lukasznowarkiewicz/low-profile-cpu-cooling-solution-research/Attachments/DD7BBE43-BE83-4B21-8B71-0276DDDCC2B3.png

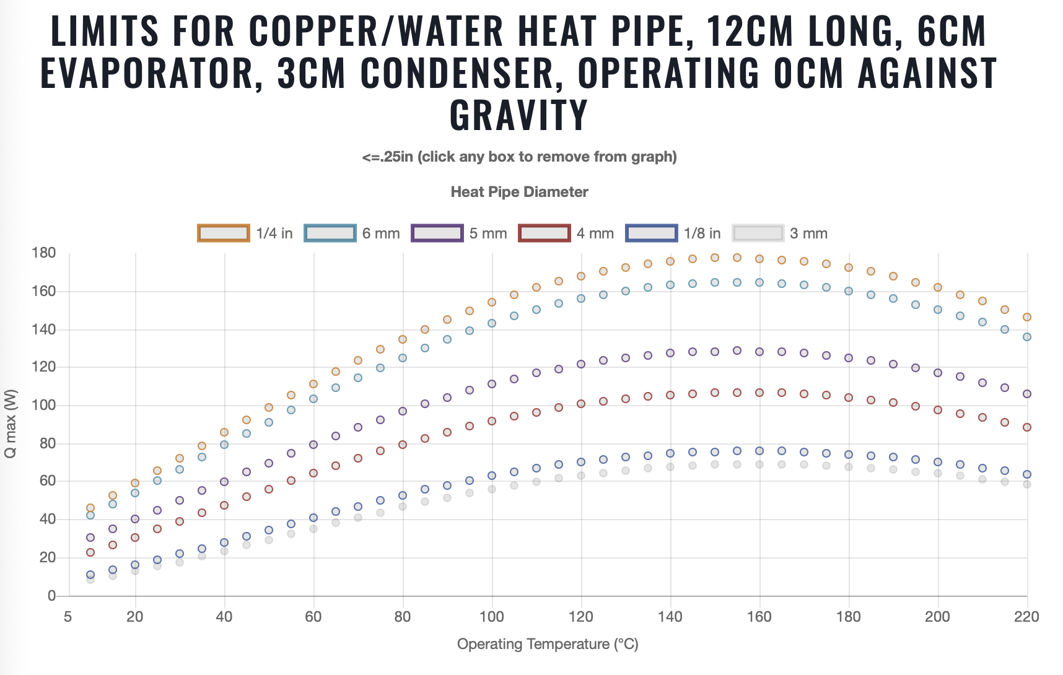
Attachments/DD7BBE43-BE83-4B21-8B71-0276DDDCC2B3.png
