lukasznowarkiewicz/low-profile-cpu-cooling-solution-research/tests recordings/series 1/Screenshot (21).png

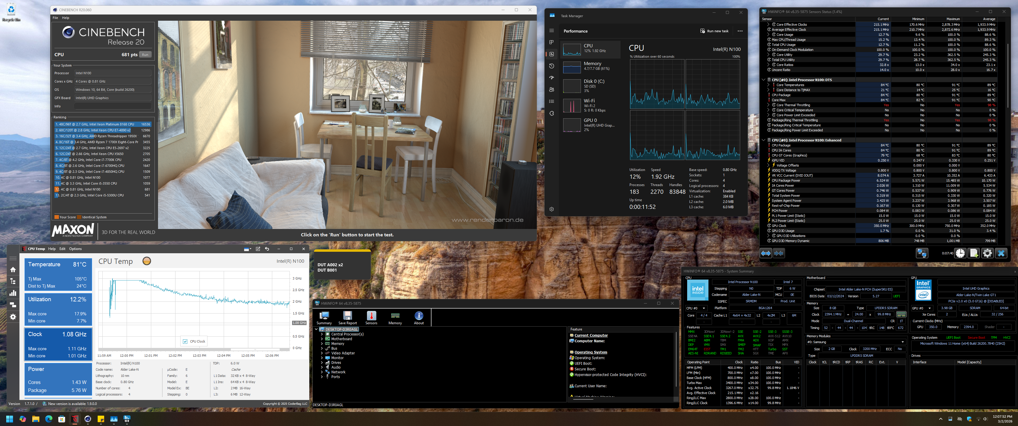
tests recordings/series 1/Screenshot (21).png
