lukasznowarkiewicz/low-profile-cpu-cooling-solution-research/tests recordings/series 3/Screenshot (115).png

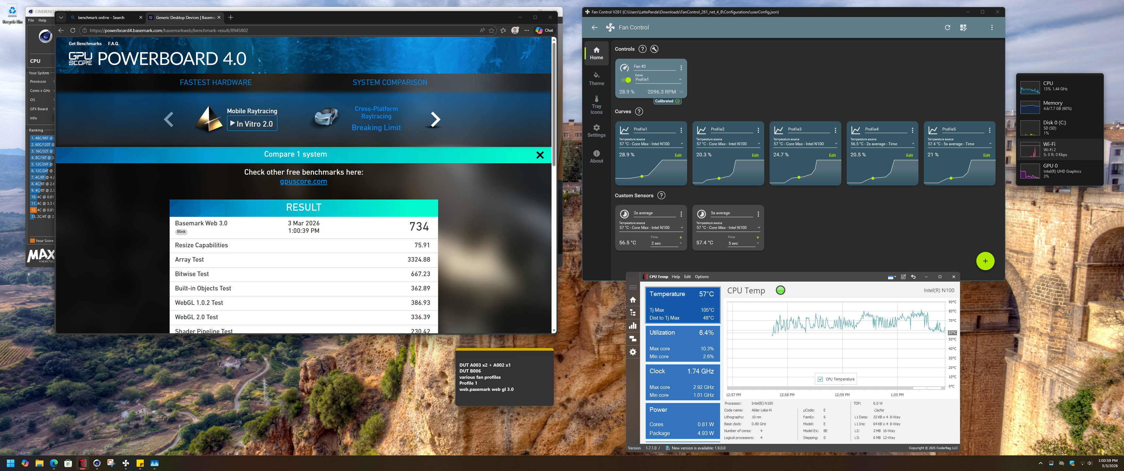
tests recordings/series 3/Screenshot (115).png
